SohanMelwani1/My-Custom-Keyboard/Assets/keycaps/stabilizer_6_25u.step

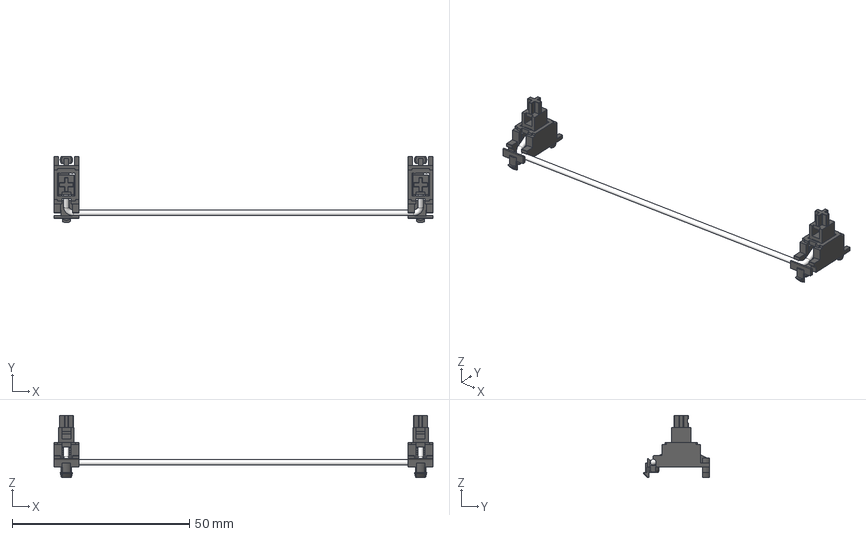
[picture p15: CAD file, 2026-09-06]
Assets/keycaps/stabilizer_6_25u.step
107.0 x 18.7 x 17.6 mm
body_l
stem_l
body_r
stem_r
wire_6_25u
