SohanMelwani1/My-Custom-Keyboard/Assets/keycaps/DSA 1.25u.step

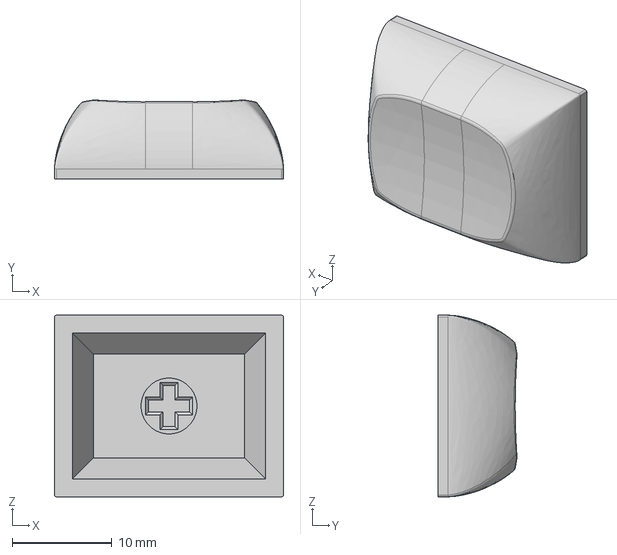
[picture p16: CAD file, 2026-09-06]
Assets/keycaps/DSA 1.25u.step
22.9 x 7.91 x 18.2 mm
