SohanMelwani1/My-Custom-Keyboard/Assets/keycaps/DSA 1.5u.step

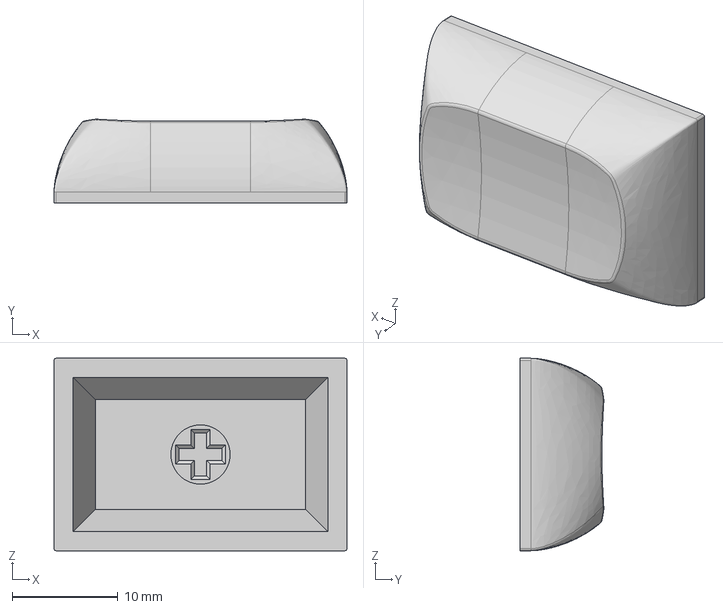
[picture p17: CAD file, 2026-09-06]
Assets/keycaps/DSA 1.5u.step
27.7 x 7.91 x 18.2 mm
