SohanMelwani1/My-Custom-Keyboard/Assets/keycaps/DSA 2u.step

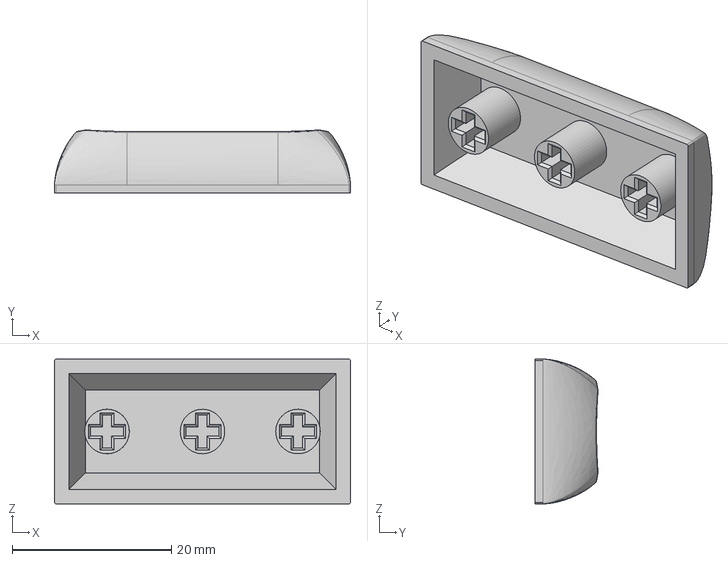
[picture p18: CAD file, 2026-09-06]
Assets/keycaps/DSA 2u.step
37.2 x 7.91 x 18.2 mm
